eldebrim/home-wellness-monitoring-network/web-app/polls/urls.py

from django.urls import path

from . import views

urlpatterns = [
    # ex: /polls/
    path('', views.index, name='index'),
    # ex: /polls/5/
    path('<int:question_id>/', views.detail, name='detail'),
    # ex: /polls/5/results/
    path('<int:question_id>/results/', views.results, name='results'),
    # ex: /polls/5/vote/
    path('<int:question_id>/vote/', views.vote, name='vote'),
    # ex: /polls/5/vote/
    path('activities/', views.activities, name='activities'),
    path('add/', views.add, name='add'),
    path('list/', views.list, name='list'),
]
